JaredButcher/cole-bot-chassis/model/freecad-20mm-aluminium-t-slot-extrusion-profile-1.snapshot.4/Choose Length (STEP)/2020 - 1m Length.step

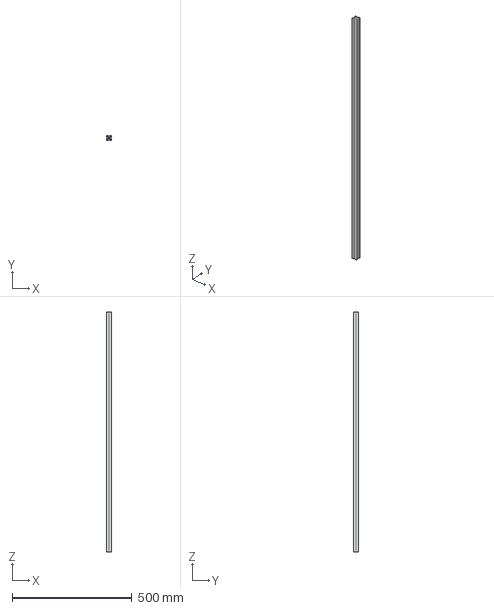
[picture p16: CAD file, 2026-10-07]
model/freecad-20mm-aluminium-t-slot-extrusion-profile-1.snapshot.4/Choose Length (STEP)/2020 - 1m Length.step
20.0 x 20.0 x 1000.0 mm
