JaredButcher/cole-bot-chassis/model/freecad-20mm-aluminium-t-slot-extrusion-profile-1.snapshot.4/Choose Length (STEP)/2020 - 10cm Length.step

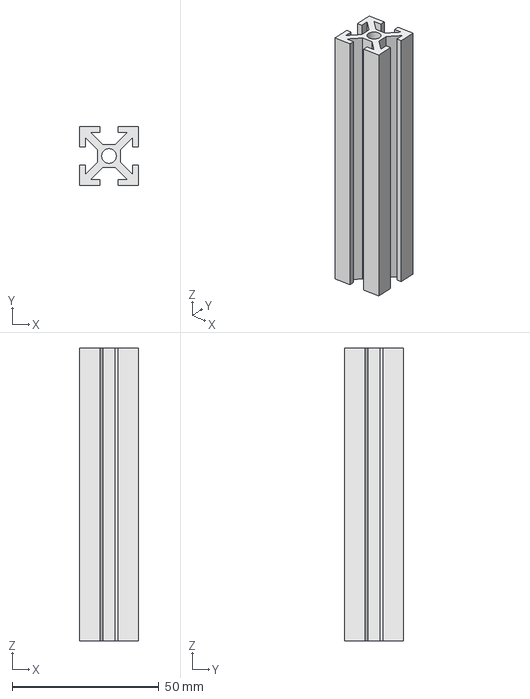
[picture p18: CAD file, 2026-10-07]
model/freecad-20mm-aluminium-t-slot-extrusion-profile-1.snapshot.4/Choose Length (STEP)/2020 - 10cm Length.step
20.0 x 20.0 x 100.0 mm
